geg-tech/pendant/art stuffs/bubble 1.png

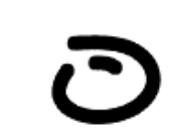
art stuffs/bubble 1.png
