geg-tech/pendant/art stuffs/pop.png

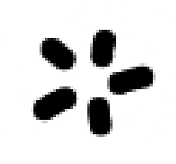
art stuffs/pop.png
