geg-tech/pendant/art stuffs/wobbly star.png

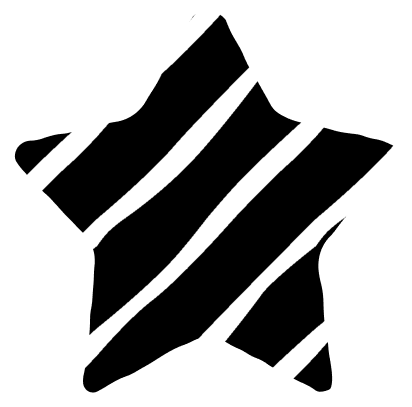
art stuffs/wobbly star.png
